worldwidemv/fes_testbed/PCB/SIM/anti_aliasing_filter.asc

C1: cap; 1n
C27: cap; 100p
C28: cap; 100p
R50: res; 11
R51: res; 11
R54: res; 10Meg
V2: voltage; 2.5
V3: voltage; 2.5
V8: voltage; ""; AC 1.; Rser=1
Named nets: 0, 2.5V, -2.5V
.MODEL DI_BAS70 D  ( IS=99.5p RS=0.600 BV=70.0 IBV=10.0u
+ CJO=2.00p  M=0.333 N=1.70 TT=7.20n
;tran 1
.ac dec 100 1 5000k
